inseven/elsewhere/models/93625A150_18-8 Stainless Steel Nylon-Insert Locknut.STEP

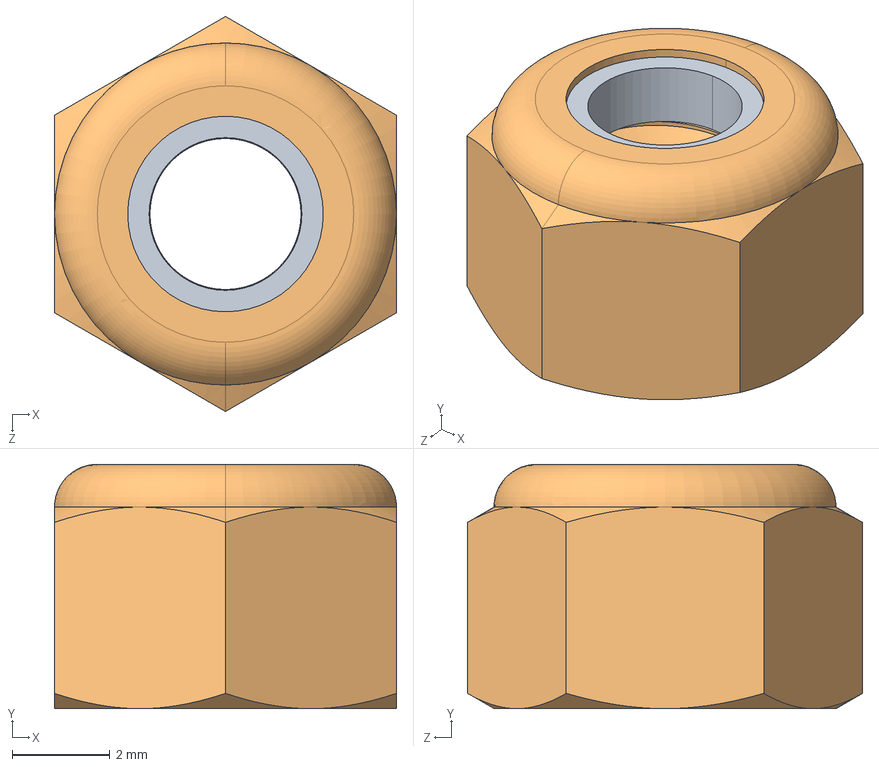
[picture p25: CAD file, 2022-01-17]
models/93625A150_18-8 Stainless Steel Nylon-Insert Locknut.STEP
7.00 x 5.00 x 8.08 mm
