inseven/elsewhere/models/91292A010_18-8 Stainless Steel Socket Head Screw.SLDPRT

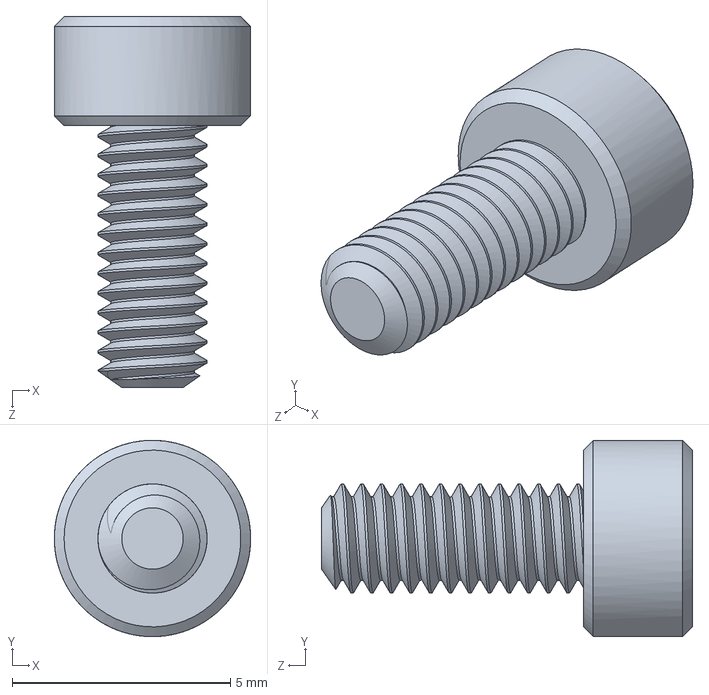
[picture p26: CAD file, 2021-11-27]
models/91292A010_18-8 Stainless Steel Socket Head Screw.SLDPRT
4.50 x 4.50 x 8.50 mm
