inseven/elsewhere/models/93615A110_18-8 Stainless Steel Low-Profile Socket Head Screw.SLDPRT

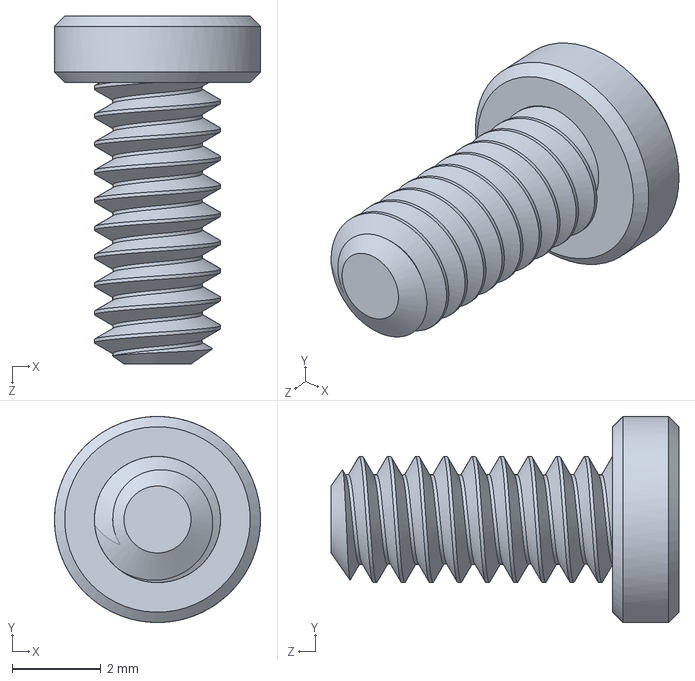
[picture p27: CAD file, 2021-11-17]
models/93615A110_18-8 Stainless Steel Low-Profile Socket Head Screw.SLDPRT
4.65 x 4.65 x 7.85 mm
