inseven/elsewhere/manufacture/v1/front.dxf

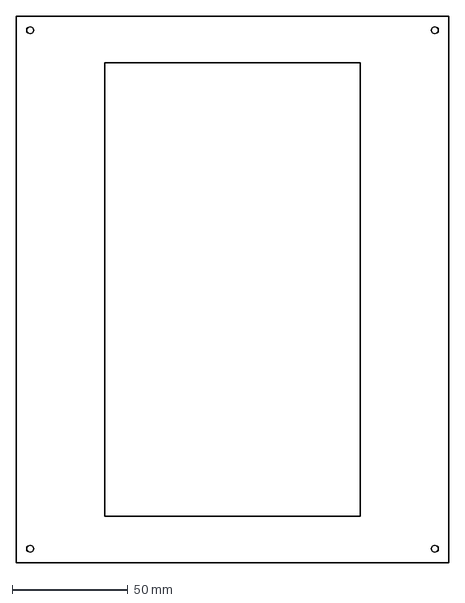
[picture p28: CAD file, 2020-08-25, an earlier design]
manufacture/v1/front.dxf
187.0 x 236.3 mm
